Chaos142/LottBespittingDiode/ref/reference_designs/adafruit_feather_ref/Adafruit Feather RP2040 USB Host.kicad_sch

## KiCad design ref/reference_designs/adafruit_feather_ref/Adafruit Feather RP2040 USB Host.kicad_sch (2026-06-01)

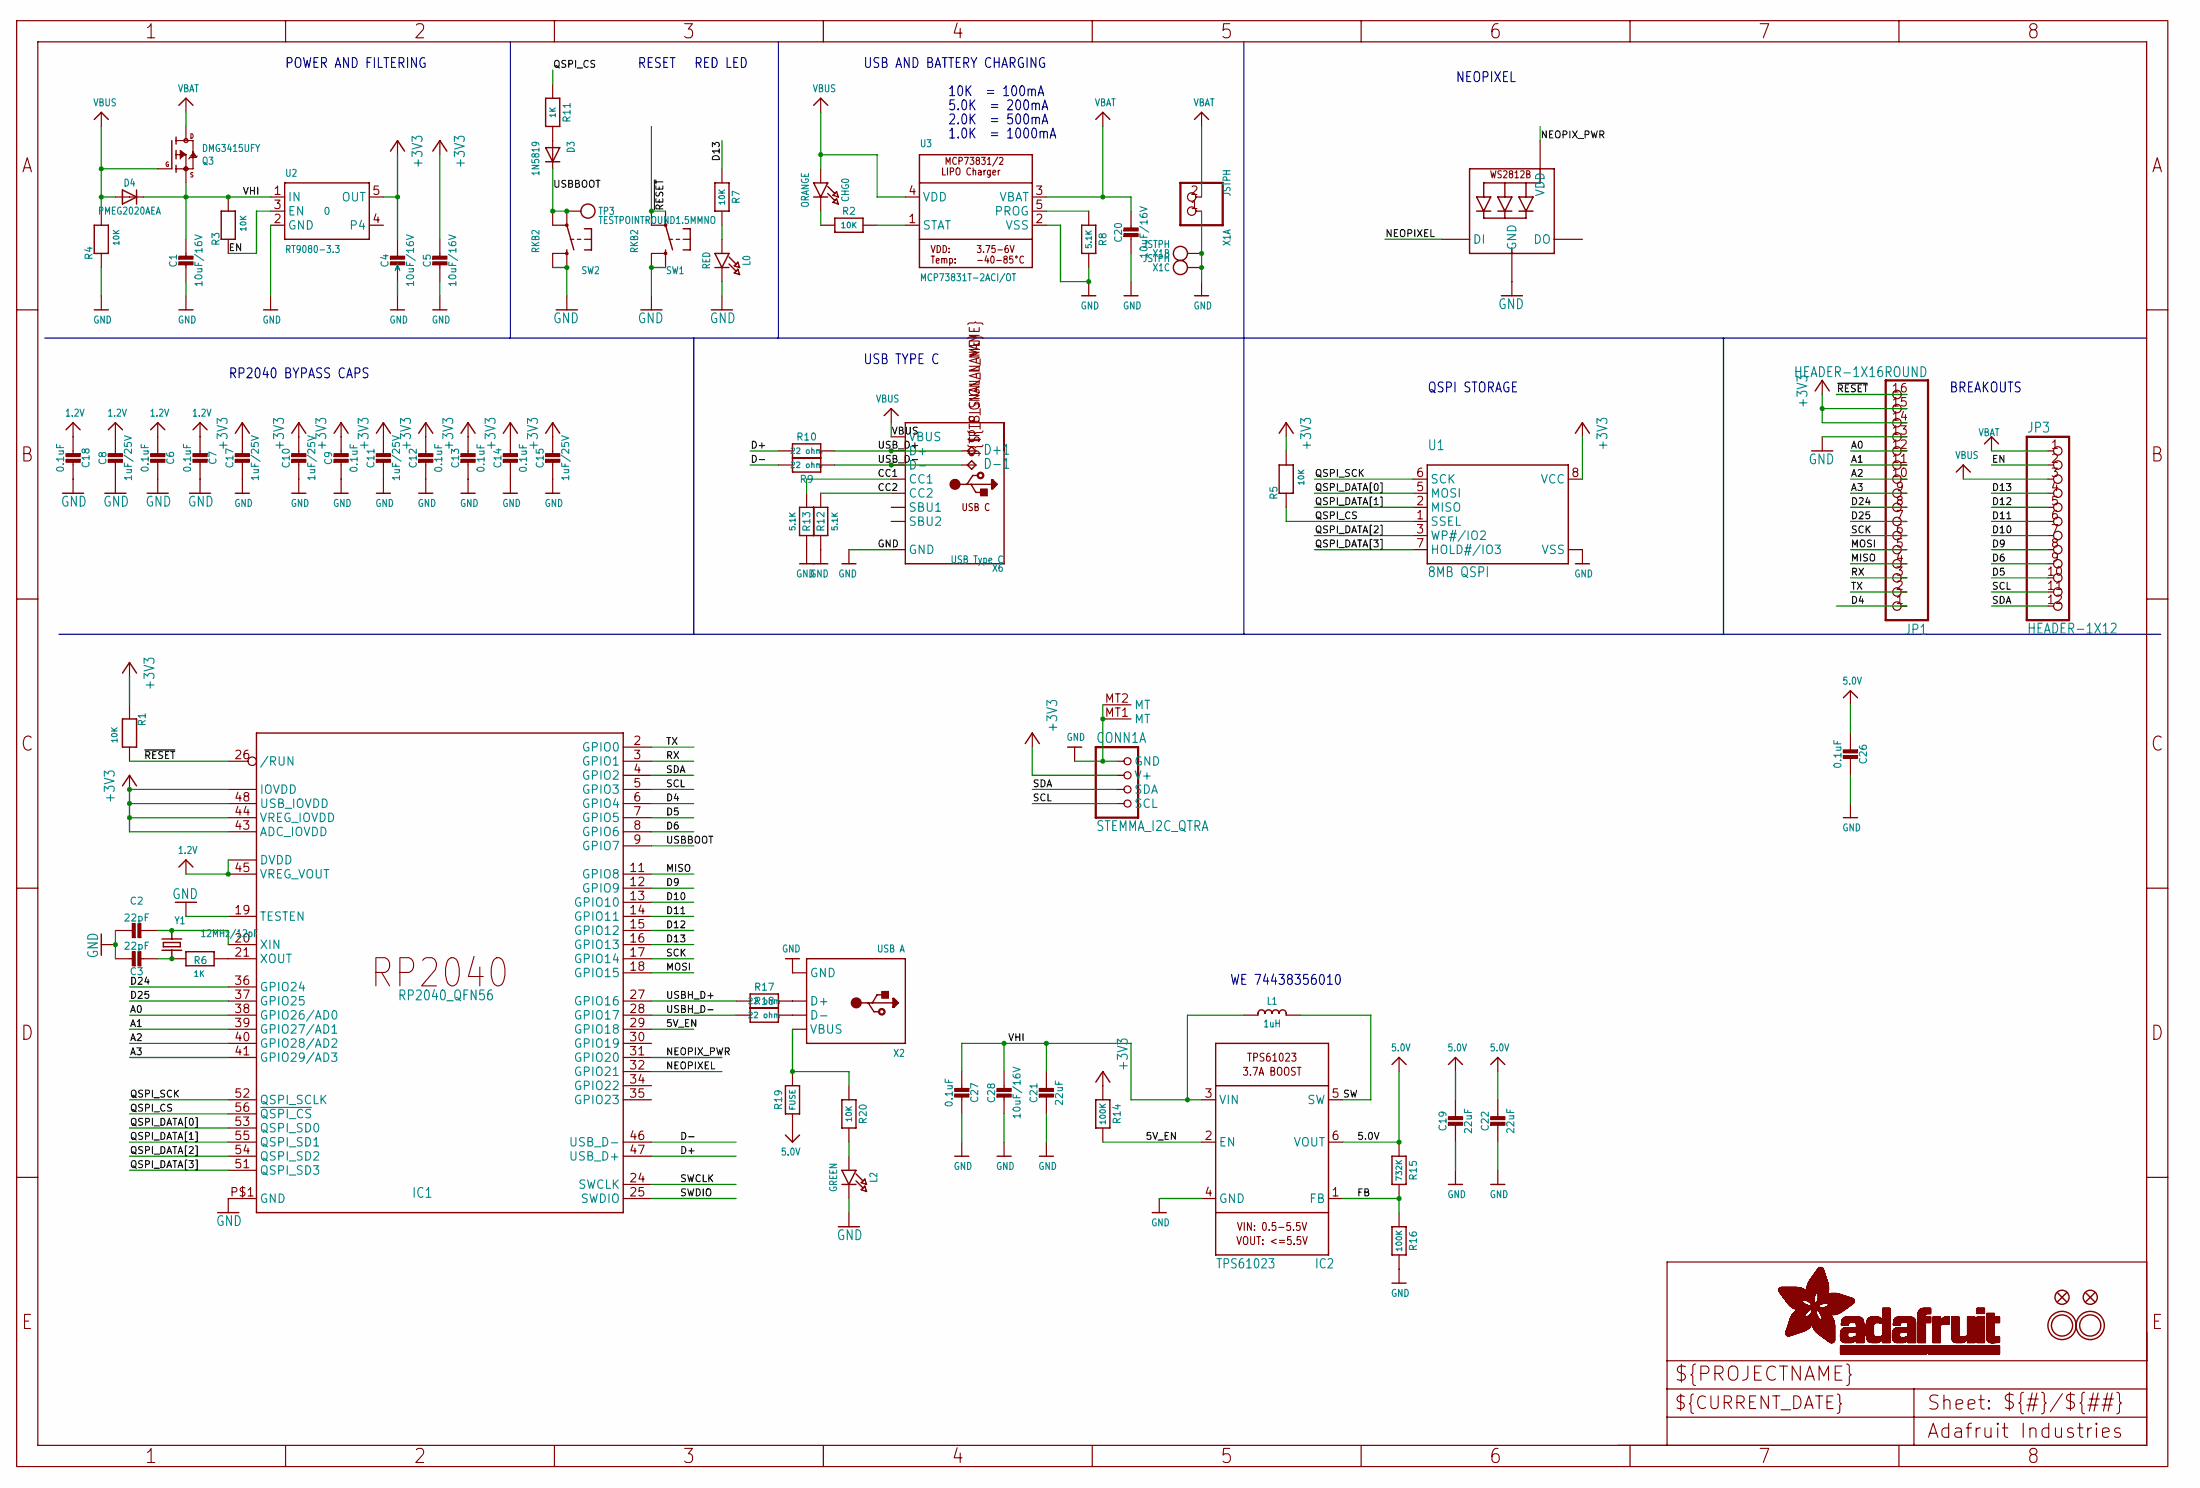
[picture p5: schematic Adafruit Feather RP2040 USB Host.kicad_sch]

Parts:
C1, C4, C5, C20, C28: 10uF/16V; 0805-NO
C2, C3: 22pF; _0402NO
C6, C7, C9, C12, C13, C14, C18, C26, C27: 0.1uF; _0402NO
C8, C10, C11, C15, C17: 1uF/25V; _0402NO
C19, C21, C22: 22uF; 0805-NO
CHG0: ORANGE; CHIPLED_0603_NOOUTLINE
CONN1: STEMMA_I2C_QTRA; JST_SH4_RA
D3: 1N5819; SOD-323_MINI
D4: PMEG2020AEA; SOD-323F
D+1: TPB1,27; B1,27
D-1: TPB1,27; B1,27
IC1: RP2040_QFN56; QFN56_7MM_REDUCEDEPAD
IC2: TPS61023; SOT563
JP1: HEADER-1X16ROUND; 1X16_ROUND
JP3: HEADER-1X12; 1X12_ROUND
L0: RED; CHIPLED_0603_NOOUTLINE
L1: 1uH; INDUCTOR_5045_SMALLTABS
L2: GREEN; CHIPLED_0603_NOOUTLINE
LED1: WS2812B_SK6805_1515; SK6805_1515
Q3: DMG3415UFY; DFN2015-3
R1, R2, R3, R4, R5, R7, R20: 10K; _0402NO
R6, R11: 1K; _0402NO
R8, R12, R13: 5.1K; _0402NO
R9, R10, R17, R18: 22 ohm; _0402NO
R14, R16: 100K; _0402NO
R15: 732K; _0402NO
R19: FUSE; 0805-NO
SW1, SW2: RKB2; BTN_RKB2_4.6X2.8
TP3: TESTPOINTROUND1.5MMNO; TESTPOINT_ROUND_1.5MM_NO
U1: 8MB QSPI; USON8_4X4
U2: RT9080-3.3; SOT23-5; JLC_ROTATION 0
U3: MCP73831T-2ACI/OT; SOT23-5
U$31, U$32: MOUNTINGHOLE2.5; MOUNTINGHOLE_2.5_PLATED
U$34, U$35: FIDUCIAL_1MM
X1: JSTPH; JSTPH2_BATT
X2: USB A; USB_HOST-SMT
X6: USB Type C; USB_C_CUSB31-CFM2AX-01-X
Y1: 12MHz/12pF; CRYSTAL_2.5X2

Connections:
1.2V: C6.2, C7.2, C8.1, C18.2, IC1.23 (DVDD), IC1.45 (VREG_VOUT), IC1.50 (DVDD)
5.0V: C19.1, C22.1, C26.2, IC2.6 (VOUT), R15.1, R19.2
5V_EN: IC1.29 (GPIO18), IC2.2 (EN), R14.2
+3V3: C4.1, C5.1, C9.1, C10.1, C11.1, C12.1, C13.1, C14.1, C15.1, C17.1, CONN1.2 (V+), IC1.1 (IOVDD), IC1.10 (IOVDD), IC1.22 (IOVDD), IC1.33 (IOVDD), IC1.42 (IOVDD), IC1.43 (ADC_IOVDD), IC1.44 (VREG_IOVDD), IC1.48 (USB_IOVDD), IC1.49 (IOVDD), JP1.14, JP1.15, R1.1, R5.2, R14.1, U1.8 (VCC), U2.5 (OUT)
A0: IC1.38 (GPIO26/AD0), JP1.12
A1: IC1.39 (GPIO27/AD1), JP1.11
A2: IC1.40 (GPIO28/AD2), JP1.10
A3: IC1.41 (GPIO29/AD3), JP1.9
CC1: R13.2, X6.A5 (CC1)
CC2: R12.2, X6.B5 (CC2)
D4: IC1.6 (GPIO4), JP1.1
D5: IC1.7 (GPIO5), JP3.10
D6: IC1.8 (GPIO6), JP3.9
D9: IC1.12 (GPIO9), JP3.8
D10: IC1.13 (GPIO10), JP3.7
D11: IC1.14 (GPIO11), JP3.6
D12: IC1.15 (GPIO12), JP3.5
D13: IC1.16 (GPIO13), JP3.4, R7.1
D24: IC1.36 (GPIO24), JP1.8
D25: IC1.37 (GPIO25), JP1.7
D+: IC1.47 (USB_D+), R10.2
D-: IC1.46 (USB_D-), R9.2
EN: JP3.2, R3.1, U2.3 (EN)
FB: IC2.1 (FB), R15.2, R16.1
GND: C1.2, C2.1, C3.1, C4.2, C5.2, C6.1, C7.1, C8.2, C9.2, C10.2, C11.2, C12.2, C13.2, C14.2, C15.2, C17.2, C18.1, C19.2, C20.2, C21.2, C22.2, C26.1, C27.1, C28.2, CONN1.1 (GND), CONN1.MT1 (MT), CONN1.MT2 (MT), IC1.19 (TESTEN), IC1.P$1 (GND), IC2.4 (GND), JP1.13, L0.C, L2.C, LED1.4 (GND), R4.1, R8.2, R12.1, R13.1, R16.2, SW1.B (S), SW1.B' (S1), SW2.B (S), SW2.B' (S1), U1.4 (VSS), U1.PAD (VSS), U2.2 (GND), U3.2 (VSS), X1.1, X1.NC1, X1.NC2, X2.GND, X6.A1B12 (GND), X6.B1A12 (GND)
MISO: IC1.11 (GPIO8), JP1.4
MOSI: IC1.18 (GPIO15), JP1.5
NEOPIXEL: IC1.32 (GPIO21), LED1.1 (DI)
NEOPIX_PWR: IC1.31 (GPIO20), LED1.2 (VDD)
unnamed: C2.2, IC1.20 (XIN), Y1.3 (2)
unnamed: C3.2, R6.1, Y1.1
unnamed: CHG0.C, R2.1
unnamed: D3.A, R11.2
unnamed: IC1.21 (XOUT), R6.2
unnamed: L0.A, R7.2
unnamed: L2.A, R20.2
unnamed: R2.2, U3.1 (STAT)
unnamed: R8.1, U3.5 (PROG)
unnamed: R17.1, X2.D+
unnamed: R18.1, X2.D-
unnamed: R19.1, R20.1, X2.VBUS
QSPI_CS: IC1.56 (~QSPI_CS), R5.1, R11.1, U1.1 (SSEL)
QSPI_DATA[0]: IC1.53 (QSPI_SD0), U1.5 (MOSI)
QSPI_DATA[1]: IC1.55 (QSPI_SD1), U1.2 (MISO)
QSPI_DATA[2]: IC1.54 (QSPI_SD2), U1.3 (WP#/IO2)
QSPI_DATA[3]: IC1.51 (QSPI_SD3), U1.7 (HOLD#/IO3)
QSPI_SCK: IC1.52 (QSPI_SCLK), U1.6 (SCK)
RX: IC1.3 (GPIO1), JP1.3
SCK: IC1.17 (GPIO14), JP1.6
SCL: CONN1.4 (SCL), IC1.5 (GPIO3), JP3.11
SDA: CONN1.3 (SDA), IC1.4 (GPIO2), JP3.12
SW: IC2.5 (SW), L1.2
SWCLK: IC1.24 (SWCLK)
SWDIO: IC1.25 (SWDIO)
TX: IC1.2 (GPIO0), JP1.2
USBBOOT: D3.C, IC1.9 (GPIO7), SW2.A, SW2.A' (P1), TP3.P$1
USBH_D+: IC1.27 (GPIO16), R17.2
USBH_D-: IC1.28 (GPIO17), R18.2
USB_D+: D+1.TP, R10.1, X6.A6 (D+), X6.B6 (D+)
USB_D-: D-1.TP, R9.1, X6.A7 (D-), X6.B7 (D-)
VBAT: C20.1, JP3.1, Q3.3 (D), U3.3 (VBAT), X1.2
VBUS: CHG0.A, D4.A, JP3.3, Q3.1 (G), R4.2, U3.4 (VDD), X6.A4B9 (VBUS), X6.B4A9 (VBUS)
VHI: C1.1, C21.1, C27.2, C28.1, D4.C, IC2.3 (VIN), L1.1, Q3.2 (S), R3.2, U2.1 (IN)
~RESET: IC1.26 (/RUN), JP1.16, R1.2, SW1.A, SW1.A' (P1)

Notes on the sheet:
RP2040 BYPASS CAPS
2.0K = 500mA
1.0K = 1000mA
USB TYPE C
QSPI STORAGE
NEOPIXEL
5.0K = 200mA
BREAKOUTS
10K = 100mA
RESET
POWER AND FILTERING
RED LED
USB AND BATTERY CHARGING
WE 74438356010
